EagleEyeElite/rgbLedCube/documentation/results/IMG_20180823_130429.jpg

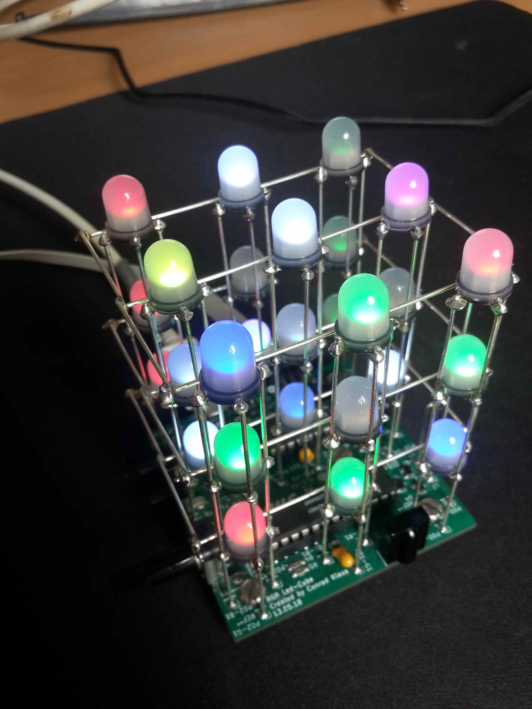
documentation/results/IMG_20180823_130429.jpg
