EagleEyeElite/rgbLedCube/documentation/results/IMG-20180820-WA0011.jpeg

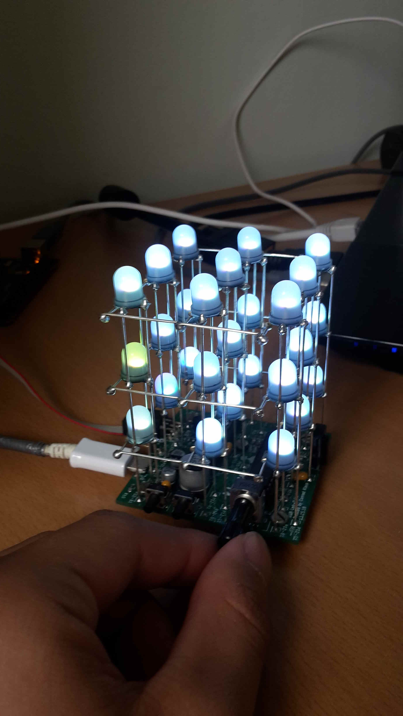
documentation/results/IMG-20180820-WA0011.jpeg
