EagleEyeElite/rgbLedCube/board/notes/20180619_152201.jpg

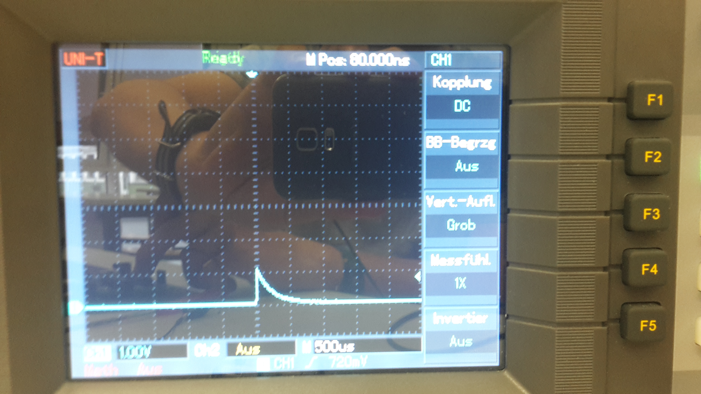
board/notes/20180619_152201.jpg
