EagleEyeElite/rgbLedCube/board/notes/20180619_152459.jpg

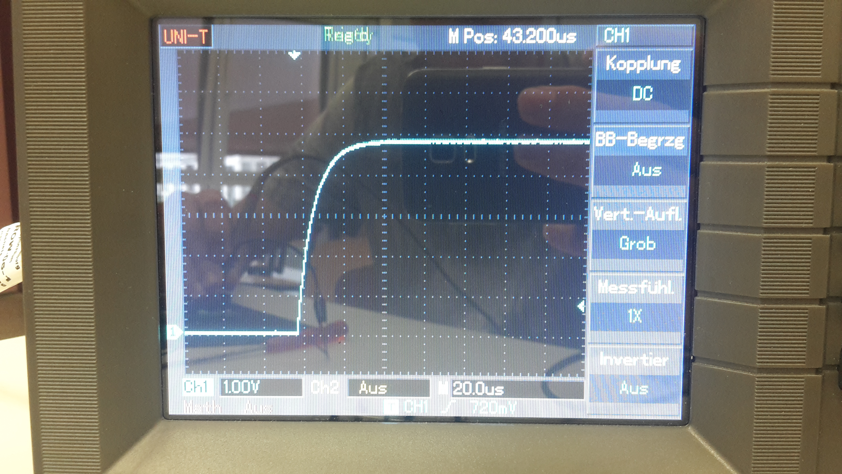
board/notes/20180619_152459.jpg
