EagleEyeElite/rgbLedCube/documentation/results/IMG-20180820-WA0002.jpeg

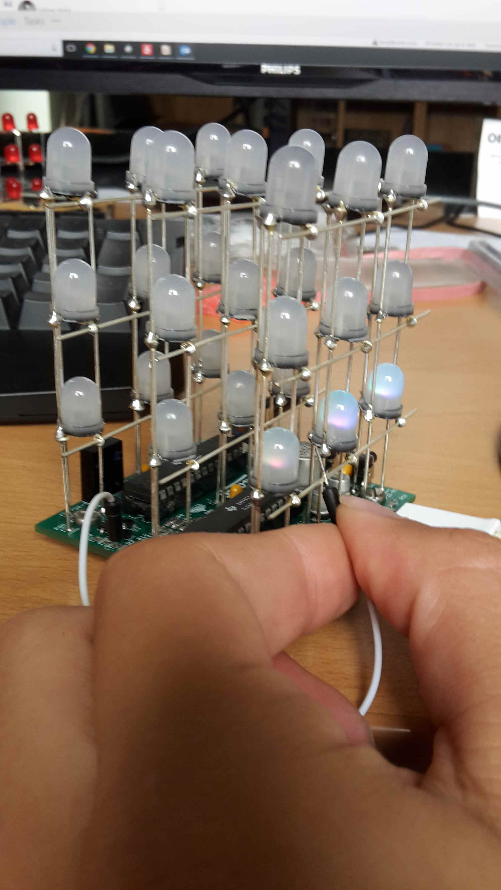
documentation/results/IMG-20180820-WA0002.jpeg
