EagleEyeElite/rgbLedCube/documentation/results/IMG-20181215-WA0003.jpeg

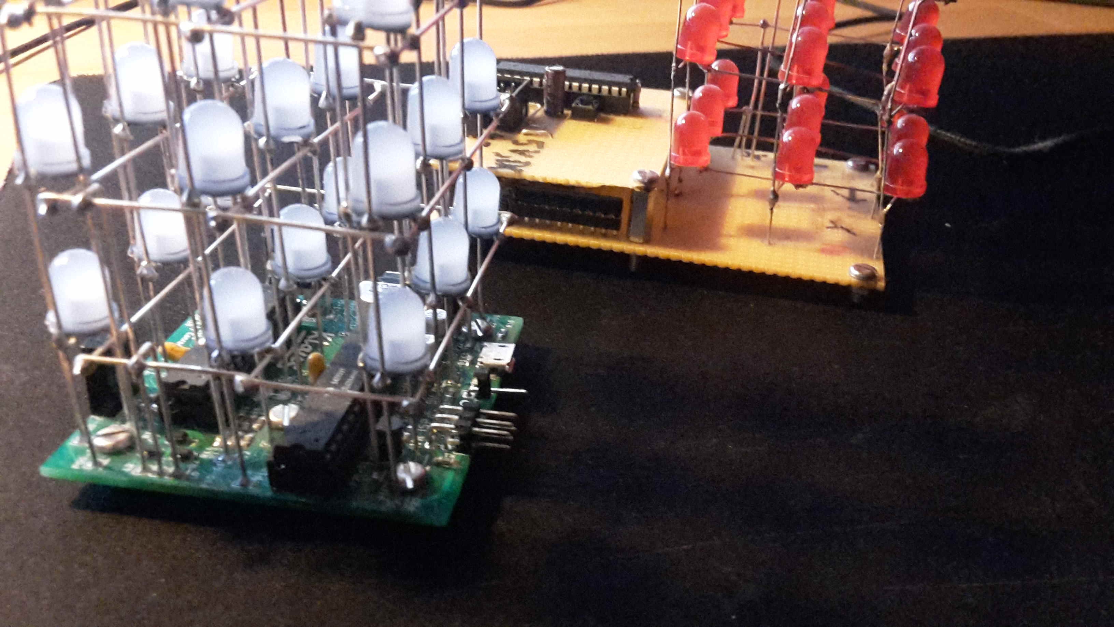
documentation/results/IMG-20181215-WA0003.jpeg
