EagleEyeElite/rgbLedCube/documentation/results/IMG_20180817_144905.jpg

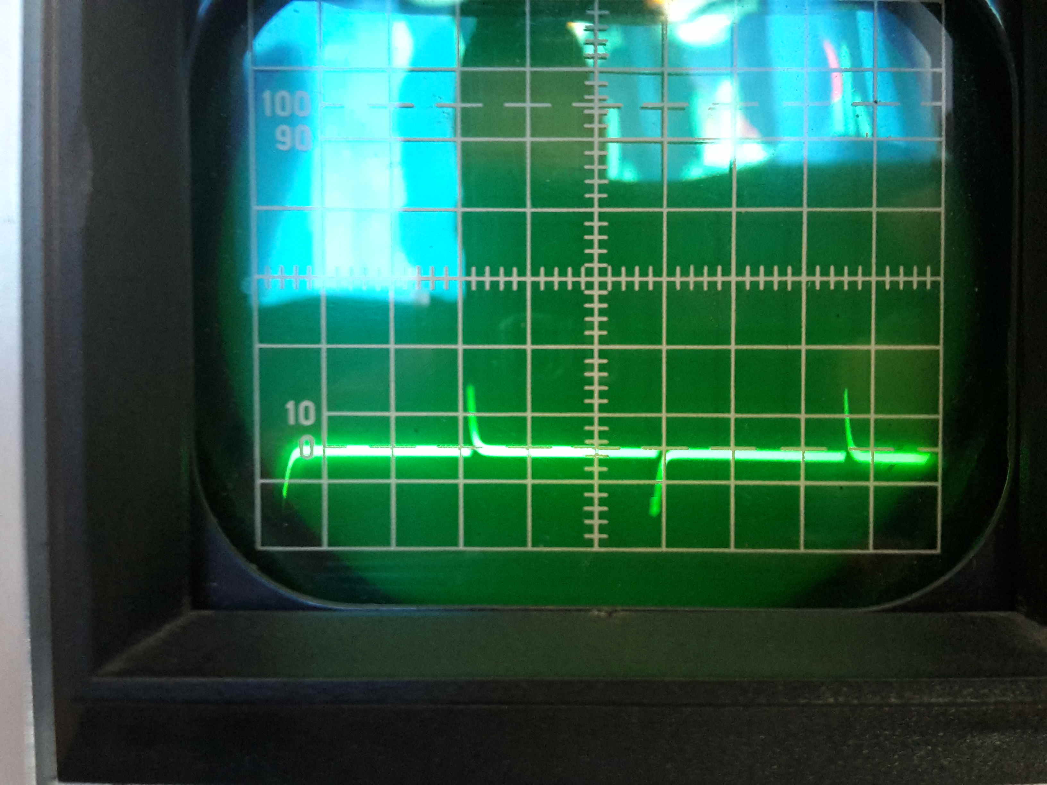
documentation/results/IMG_20180817_144905.jpg
