EagleEyeElite/rgbLedCube/documentation/results/IMG_20180817_222203.jpg

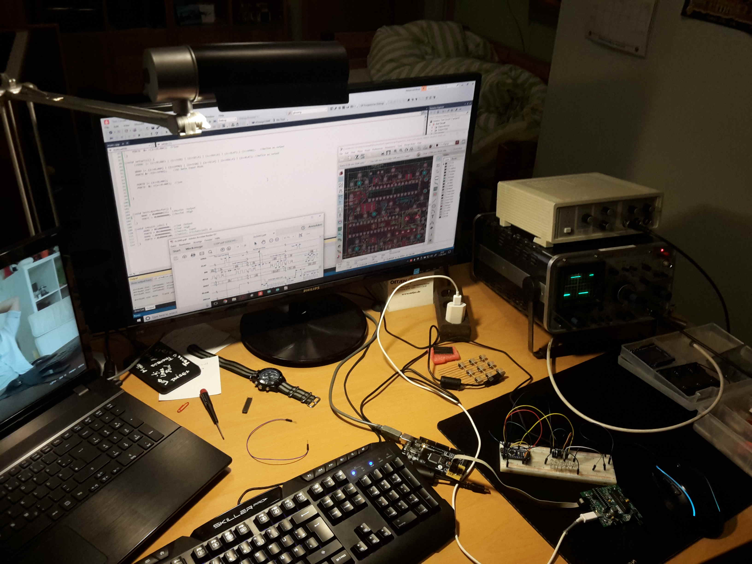
documentation/results/IMG_20180817_222203.jpg
