EagleEyeElite/rgbLedCube/documentation/results/IMG_20180823_130444.jpg

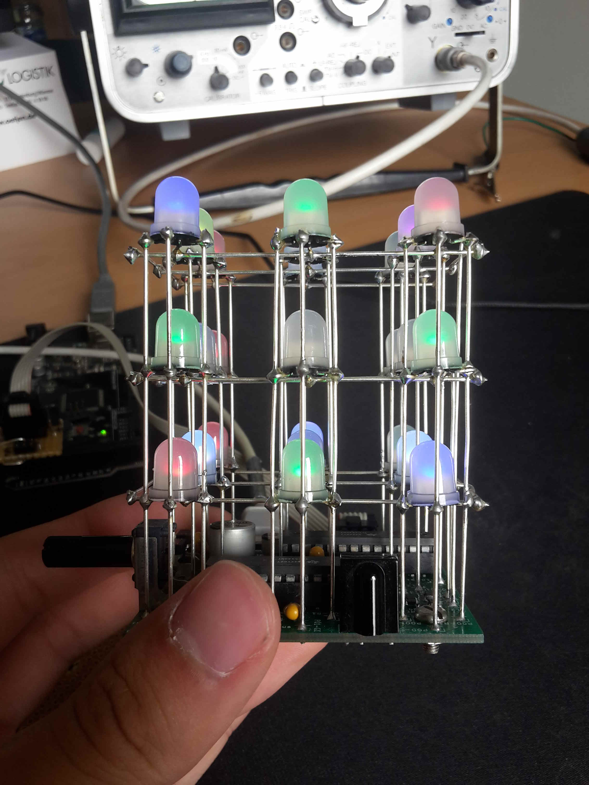
documentation/results/IMG_20180823_130444.jpg
