EagleEyeElite/rgbLedCube/documentation/results/IMG_20180823_130459.jpg

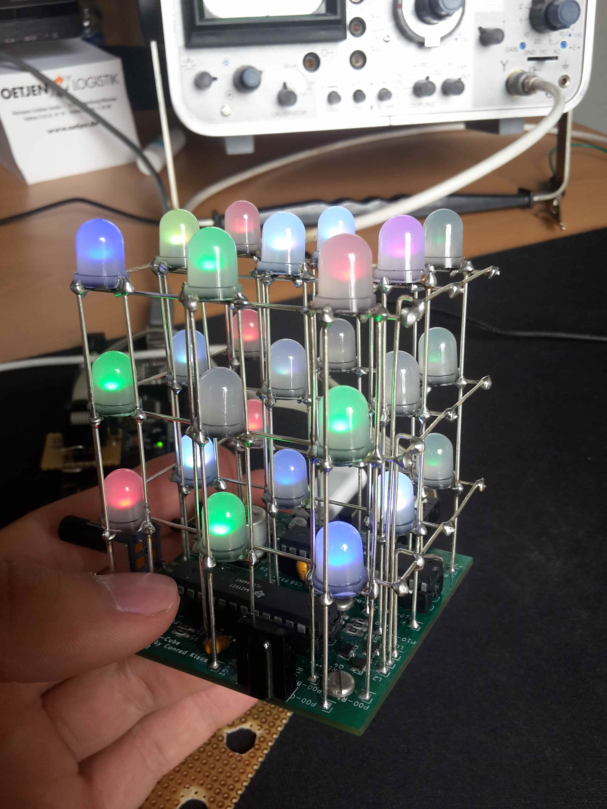
documentation/results/IMG_20180823_130459.jpg
