EagleEyeElite/rgbLedCube/code/src/hardware/driver/timer0.c

//
// Created by Conrad Klaus on 06.06.22.
//

#include "timer0.h"

#include "../pinLayout.h"
#include "layerMosfets.h"
#include "usart.h"
#include <avr/io.h>
#include <avr/interrupt.h>


void startLayerSwitching() {
    // control MSPIM - timer 0 interrupts: CTC mode, timer 0 interrupt on OCR2A, 1024 prescaler
    // interrupt after 3.2768ms, 101.7 hz refresh rate
    TCCR0A |= 1 << WGM01;
    OCR0A = 64;     // prescaler*OCR0A /20MHZ -> interrupt timing
    TIMSK0 |= 1 << OCIE0A;
    TCCR0B |= 1 << CS00 | 1 << CS02;    // start timer
}

void stopLayerSwitching() {
    TCCR0B &= ~(1 << CS00 | 1 << CS02); // stops timer 0
    TIFR0 |= 1<<OCF0A;  // clear Timer0 Output Compare A Match Flag
}

static uint8_t currentLayer = 0;

/**
 * The interrupt handles the display layer switching.
 * Preloaded data of the current layer is latched into the Led Driver and
 * the current layer gets enabled.
 * It also triggers the loading of the led driver with next layer data.
 */
ISR(TIMER0_COMPA_vect, ISR_BLOCK) {    // controls MSPIM upload and cube image
    TCNT0 = 0;    // resets Counter
    PIND = 1 << BLANK;    // high (inverted) - resets TLC counter (4096)
    PIND = 1 << XLAT;    // latches new Data
    PIND = 1 << XLAT;
    setMosfets(currentLayer++);
    // blank goes low to start the next cycle, TLC will start to recount
    // make sure there is a 1µS delay before switching it again! (PCB board inverter)
    PIND = 1 << BLANK; // low (inverted)

    if (currentLayer > 2) {
        currentLayer = 0;
    }
    startTransmission(currentLayer);
}
