EagleEyeElite/rgbLedCube/code/src/interface/Frame.h

/* 
* Frame.h
*
* Created: 02.09.2018 19:28:43
* Author: Conrad
*/

#include <avr/io.h>
#include "../hardware/display.h"

#pragma once


class Frame {
public:
    explicit Frame(bool smooth);

    bool smooth;    // sets render option for addLight

    void loadImage(unsigned int imageNr);    // loads image from IMG_preset.h

    void getLed(unsigned int ledNr, uint8_t rgb[3]);

    void addLight(const float *koo, const uint8_t *rgb);

    void addLight(uint8_t ledNr, const uint8_t *rgb);

    void addFrame(Frame Frame_to_add);    // adds a Frame to current Frame
    void resetFrame();

    void showFrame();    // displays Frame
    //~Frame();
private:
    void writeFrame(const uint8_t koo[3], const uint8_t rgb[3]);

    imageData ledFrameColours; // 24-bit Color resolution
}; //Frame
