EagleEyeElite/rgbLedCube/code/src/interface/img_preset.h

/*
 * IMG_preset.h
 *
 * Created: 30/09/2018 20:53:01
 *  Author: Conrad
 */

#include <avr/pgmspace.h>
#include <avr/io.h>
#include "../hardware/display.h"

#pragma once

const PROGMEM imageData image_Preset[] = {
        //Image 0 - empty image
        {   //	L1 r, L1 g,	L1 b, L2 r, L2 g, L2 b,	L3 r, L3 g, L3 b, L4 r, L4 g, L4 b,	L5 r, L5 g, L5 b, L6 r, L6 g, L6 b,	L7 r, L7 g, L7 b, L8 r, L8 g, L8 b,	L9 r, L9 g, L9 b	//Led 1 Red...
                0x00, 0x00, 0x00, 0x00, 0x00, 0x00, 0x00, 0x00, 0x00, 0x00, 0x00, 0x00, 0x00, 0x00, 0x00, 0x00, 0x00, 0x00, 0x00, 0x00, 0x00, 0x00, 0x00, 0x00, 0x00, 0x00, 0x00,   //Layer 1
                0x00, 0x00, 0x00, 0x00, 0x00, 0x00, 0x00, 0x00, 0x00, 0x00, 0x00, 0x00, 0x00, 0x00, 0x00, 0x00, 0x00, 0x00, 0x00, 0x00, 0x00, 0x00, 0x00, 0x00, 0x00, 0x00, 0x00,   //Layer 2
                0x00, 0x00, 0x00, 0x00, 0x00, 0x00, 0x00, 0x00, 0x00, 0x00, 0x00, 0x00, 0x00, 0x00, 0x00, 0x00, 0x00, 0x00, 0x00, 0x00, 0x00, 0x00, 0x00, 0x00, 0x00, 0x00, 0x00,   //Layer 3
        },
        //Image 1 - a few random colours
        {   //	L1 r, L1 g,	L1 b, L2 r, L2 g, L2 b,	L3 r, L3 g, L3 b, L4 r, L4 g, L4 b,	L5 r, L5 g, L5 b, L6 r, L6 g, L6 b,	L7 r, L7 g, L7 b, L8 r, L8 g, L8 b,	L9 r, L9 g, L9 b	//Led 1 Red...
                0xFF, 0x00, 0x00, 0xFF, 0xFF, 0xFF, 0x00, 0x00, 0x00, 0x00, 0x00, 0x00, 0x00, 0x00, 0x00, 0x00, 0x00, 0x00, 0x00, 0x00, 0x00, 0x00, 0x00, 0x00, 0x00, 0x00, 0x00,   //Layer 1
                0x00, 0xFF, 0x00, 0x00, 0x00, 0x00, 0x00, 0x00, 0x00, 0x00, 0x00, 0x00, 0x00, 0x00, 0x00, 0x00, 0x00, 0x00, 0x00, 0x00, 0x00, 0x00, 0x00, 0x00, 0x00, 0x00, 0x00,   //Layer 2
                0x00, 0x00, 0xFF, 0x00, 0x00, 0x00, 0x00, 0x00, 0x00, 0x00, 0x00, 0x00, 0x00, 0x00, 0x00, 0x00, 0x00, 0x00, 0x00, 0x00, 0x00, 0x00, 0x00, 0x00, 0x00, 0x00, 0x00,   //Layer 3
        },
        //Image 2 - a lot random colours
        {   //  L1 r, L1 g,	L1 b, L2 r, L2 g, L2 b,	L3 r, L3 g, L3 b, L4 r, L4 g, L4 b,	L5 r, L5 g, L5 b, L6 r, L6 g, L6 b,	L7 r, L7 g, L7 b, L8 r, L8 g, L8 b,	L9 r, L9 g, L9 b	//Led 1 Red...
                0xFF, 0x00, 0x00, 0x00, 0xFF, 0x00, 0x00, 0x00, 0xFF, 0xFF, 0x00, 0xAF, 0xFF, 0xFF, 0xFF, 0xEF, 0xFF, 0x00, 0x00, 0x55, 0x00, 0xFF, 0xFF, 0xFF, 0xFF, 0x00, 0x00,   //Layer 1
                0x00, 0xFF, 0x00, 0x00, 0x00, 0x00, 0x00, 0xFF, 0x00, 0x00, 0x00, 0x00, 0x5F, 0x5F, 0x5F, 0x8F, 0x8F, 0x8F, 0x00, 0x55, 0x00, 0x00, 0x00, 0x00, 0xFF, 0x00, 0x00,   //Layer 2
                0x00, 0x00, 0xFF, 0x00, 0xFF, 0x00, 0xFF, 0x00, 0x00, 0xFF, 0xFF, 0xFF, 0x00, 0x3F, 0x8F, 0xFF, 0xFF, 0xFF, 0x00, 0x55, 0x00, 0xFF, 0xFF, 0xFF, 0xFF, 0x00, 0x00,   //Layer 3
        }
};
