EagleEyeElite/rgbLedCube/code/src/hardware/driver/layerMosfets.h

/**
 * The mosfets enable and disable the layers of the led cube.
 */

#pragma once

#include <stdint.h>

#ifdef __cplusplus
extern "C" {
#endif

void initDisplayLayerMosfets();
void setMosfets(uint8_t layer);
void disableDisplayLayerMosfets();

#ifdef __cplusplus
}
#endif
