EagleEyeElite/rgbLedCube/code/src/hardware/driver/timer1.h

/**
 * Timer1 generates a clock signal for the led driver.
 * The clock signal connects to GSCLK of the TLC5940.
 */

#pragma once

#include <stdint.h>
#include <stdint-gcc.h>

#ifdef __cplusplus
extern "C" {
#endif

void startGSCLK();
void stopGSCLK();

#ifdef __cplusplus
}
#endif
