EagleEyeElite/rgbLedCube/documentation/results/IMG_20180818_181341.jpg

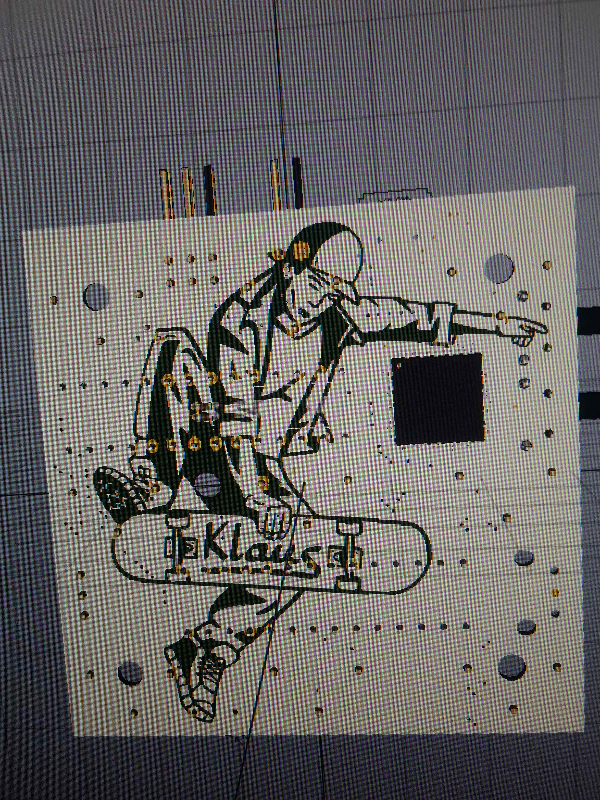
documentation/results/IMG_20180818_181341.jpg
